liwenyip/adhoc/Appendix A - Figures/Diagrams/Buffer-Structure.gif

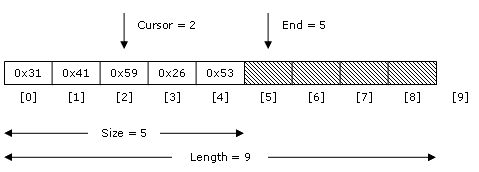
Appendix A - Figures/Diagrams/Buffer-Structure.gif
