liwenyip/adhoc/Appendix A - Figures/Diagrams/Manchester Signal.gif

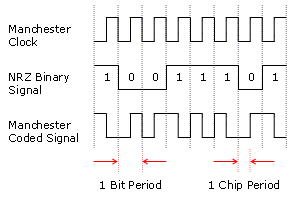
Appendix A - Figures/Diagrams/Manchester Signal.gif
