liwenyip/adhoc/Appendix A - Figures/Diagrams/Screenshot-Receive.gif

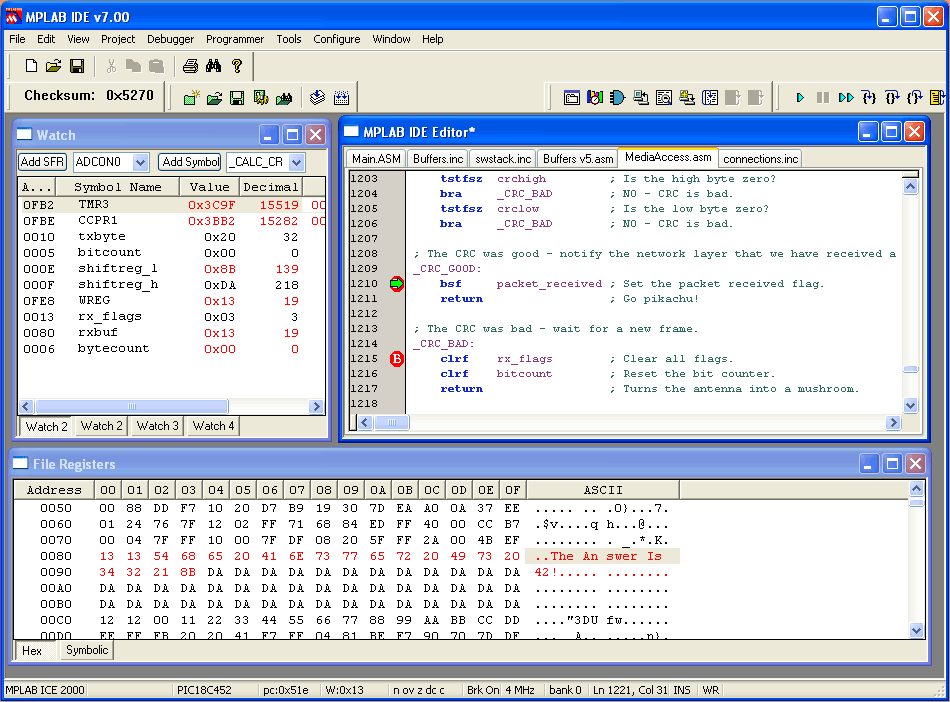
Appendix A - Figures/Diagrams/Screenshot-Receive.gif
