liwenyip/adhoc/Appendix A - Figures/Flowcharts/Decode.jpg

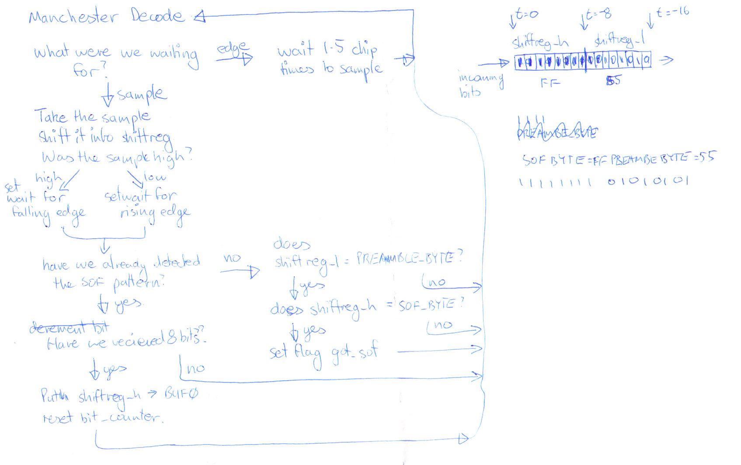
Appendix A - Figures/Flowcharts/Decode.jpg
