liwenyip/adhoc/Appendix A - Figures/Flowcharts/Encode.jpg

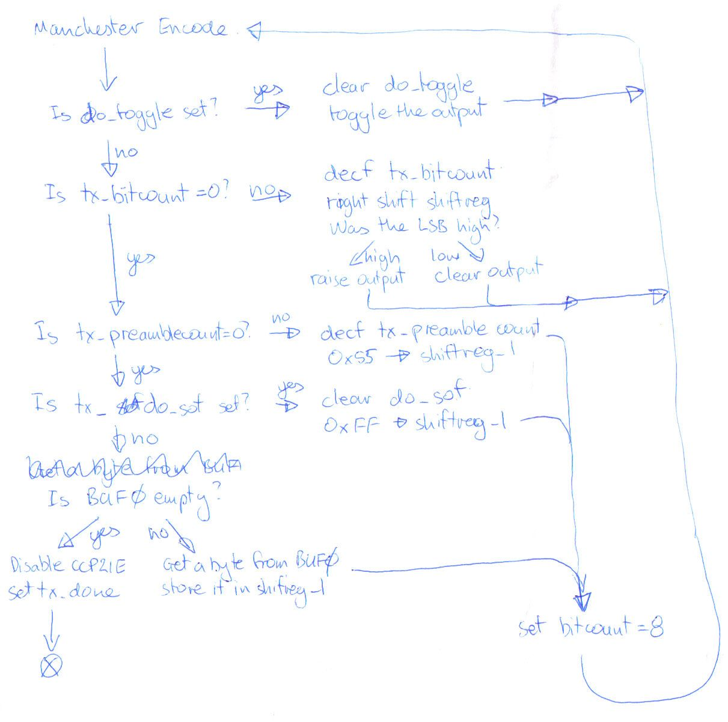
Appendix A - Figures/Flowcharts/Encode.jpg
