liwenyip/adhoc/Appendix A - Figures/Hardware/2004-Hardware-Block-Diagram.jpg

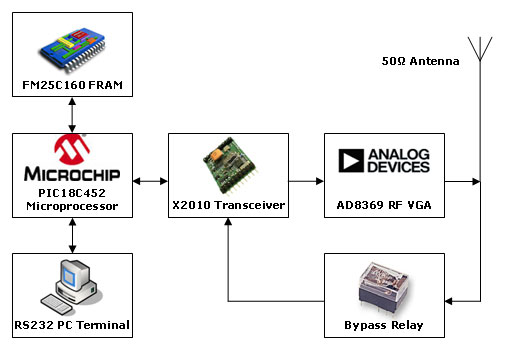
Appendix A - Figures/Hardware/2004-Hardware-Block-Diagram.jpg
