liwenyip/adhoc/Appendix A - Figures/Hardware/Emitter Follower.gif

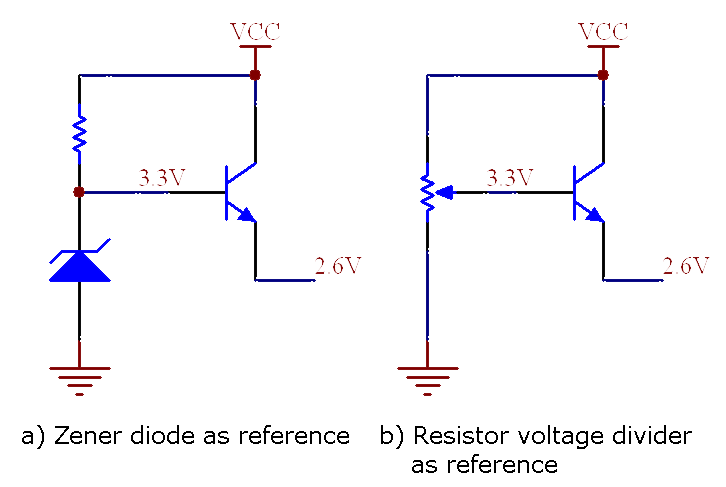
Appendix A - Figures/Hardware/Emitter Follower.gif
