liwenyip/adhoc/Appendix A - Figures/Hardware/OffSeparation-1.jpg

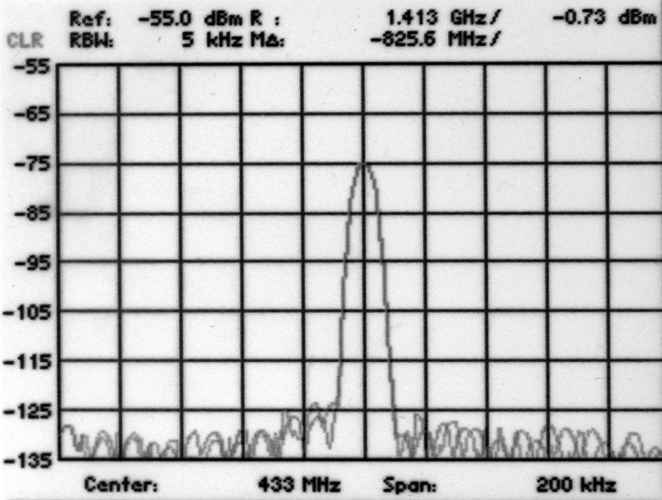
Appendix A - Figures/Hardware/OffSeparation-1.jpg
