liwenyip/adhoc/Appendix A - Figures/Hardware/OffSeparation-2.jpg

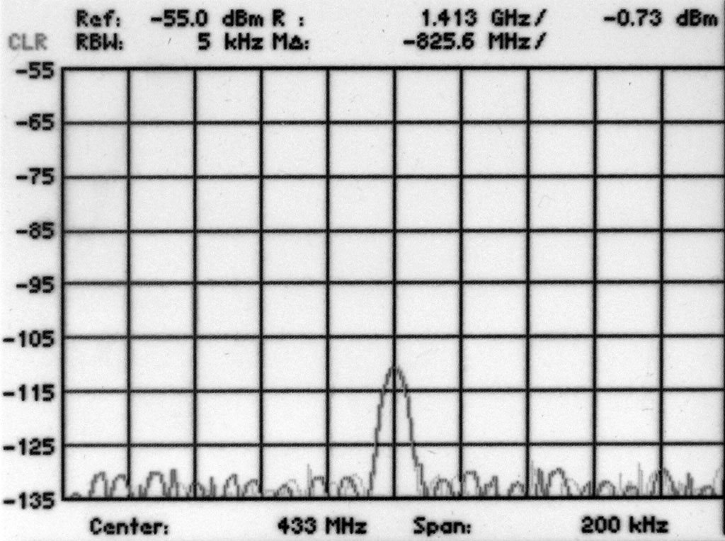
Appendix A - Figures/Hardware/OffSeparation-2.jpg
