liwenyip/adhoc/Appendix A - Figures/Hardware/PCB-Rev-3.jpg

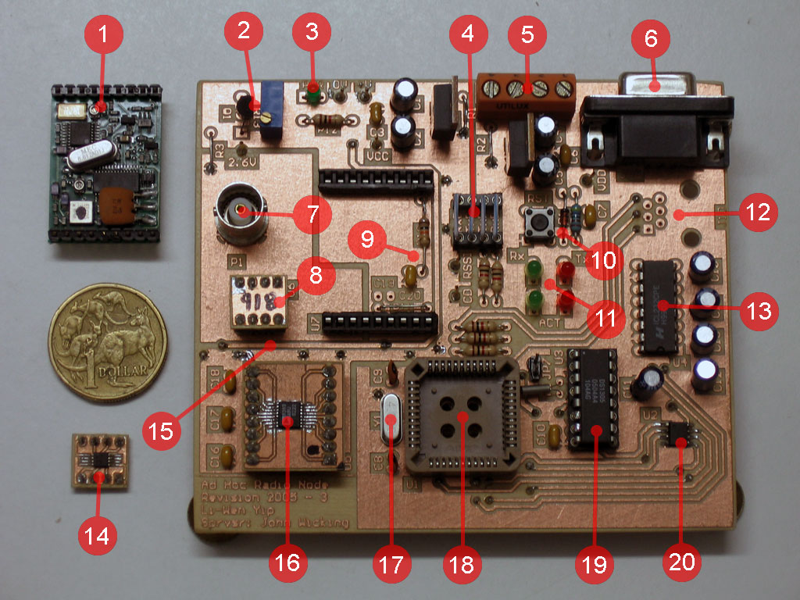
Appendix A - Figures/Hardware/PCB-Rev-3.jpg
