liwenyip/adhoc/Appendix A - Figures/Manchester Coding/Clock Detect Timing Diagram.gif

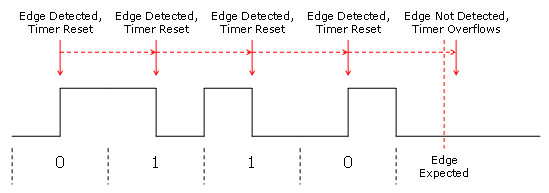
Appendix A - Figures/Manchester Coding/Clock Detect Timing Diagram.gif
