liwenyip/adhoc/Appendix A - Figures/Manchester Coding/Clock Drift.gif

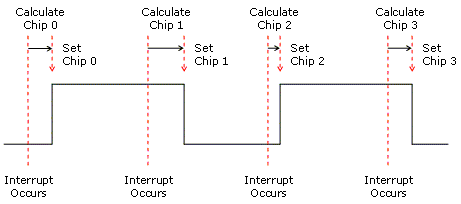
Appendix A - Figures/Manchester Coding/Clock Drift.gif
