liwenyip/adhoc/Appendix A - Figures/Manchester Coding/Sync Logic Timing Diagram.GIF

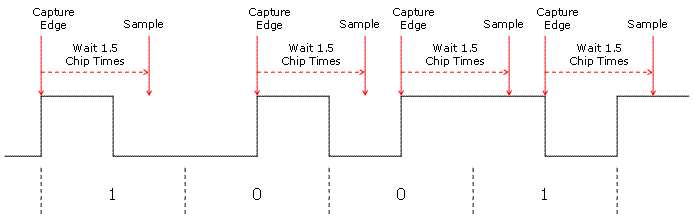
Appendix A - Figures/Manchester Coding/Sync Logic Timing Diagram.GIF
