liwenyip/adhoc/Appendix A - Figures/Photos/Carrier Detect, 1ms-div, 5v-div.jpg

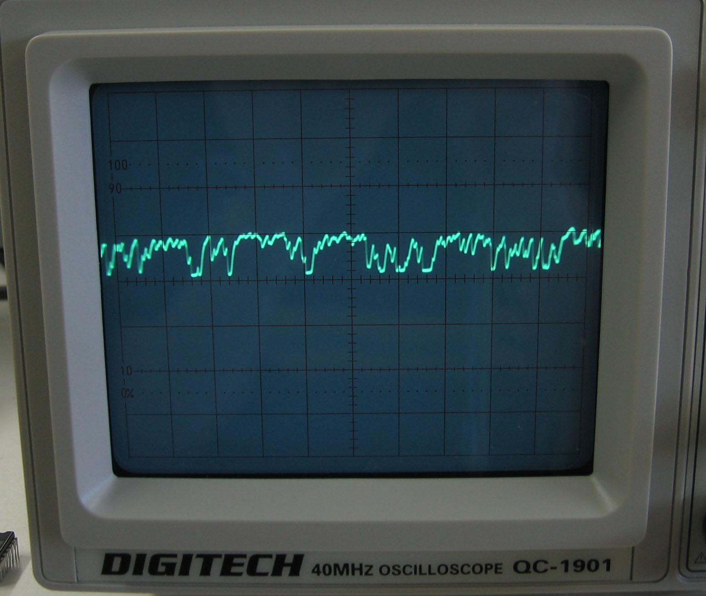
Appendix A - Figures/Photos/Carrier Detect, 1ms-div, 5v-div.jpg
