liwenyip/adhoc/Appendix A - Figures/Photos/PCB Revision 1.jpg

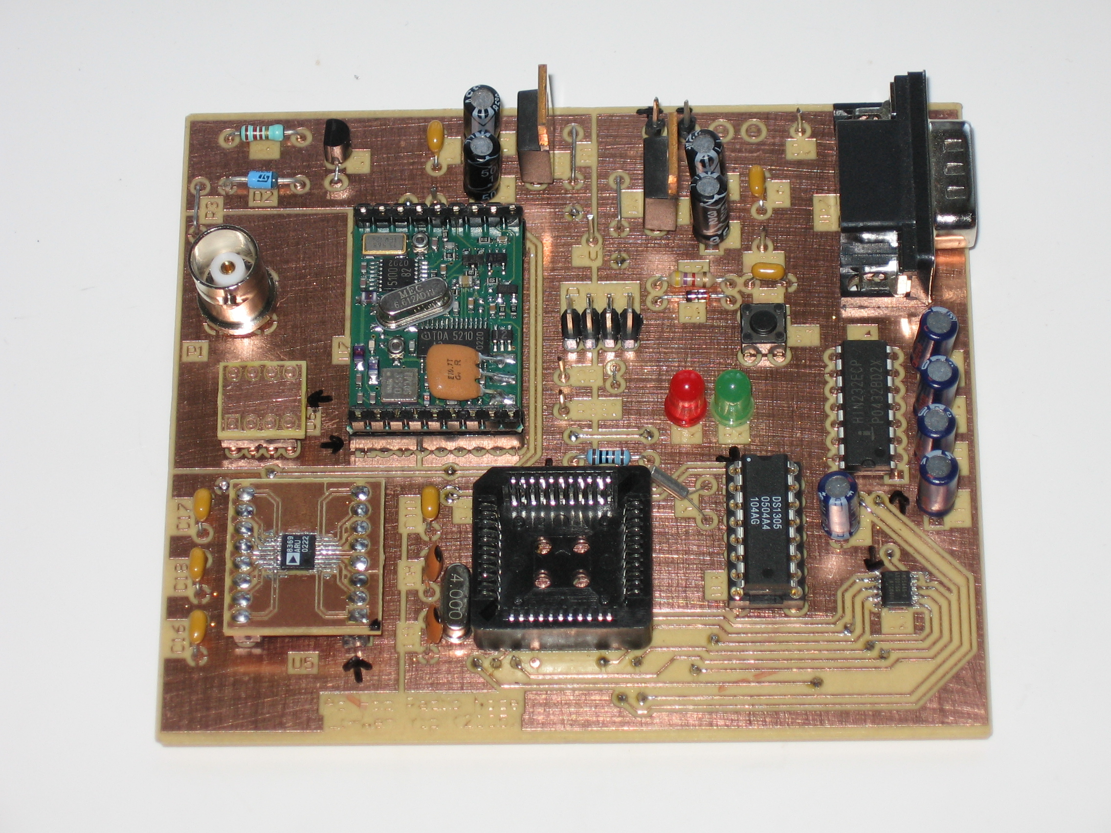
Appendix A - Figures/Photos/PCB Revision 1.jpg
