liwenyip/adhoc/Appendix A - Figures/Photos/Port separation 1.jpg

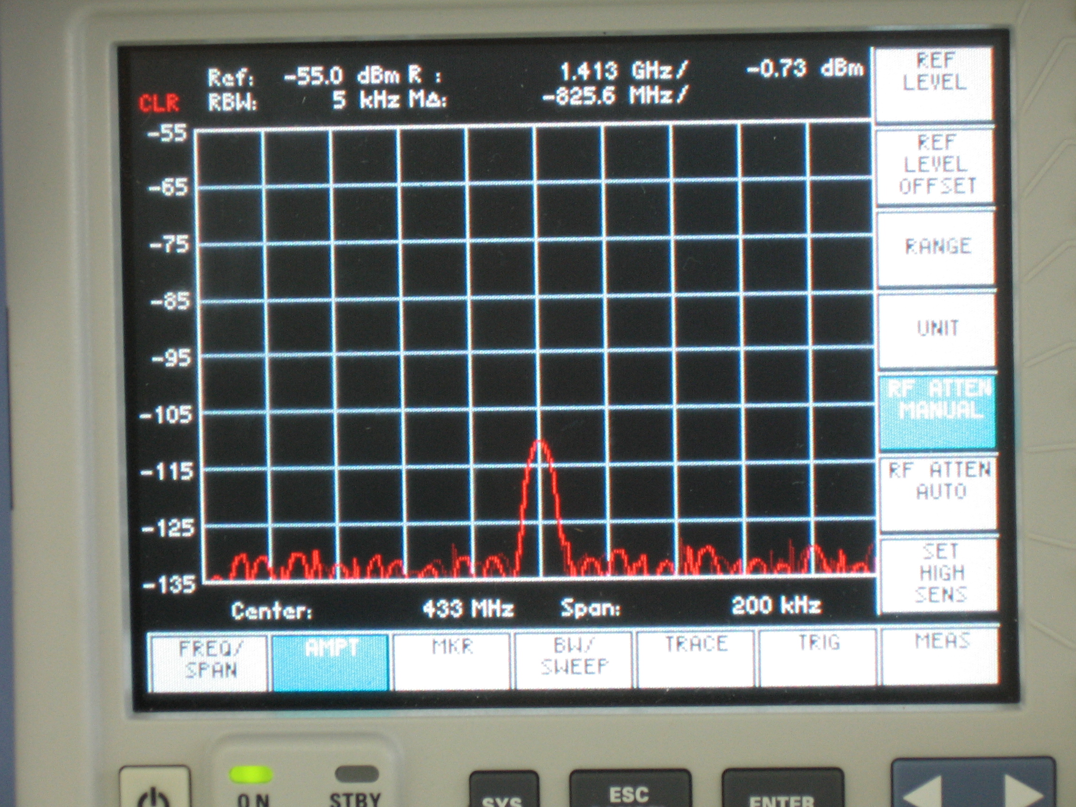
Appendix A - Figures/Photos/Port separation 1.jpg
