liwenyip/adhoc/Appendix A - Figures/Photos/Port separation 2.jpg

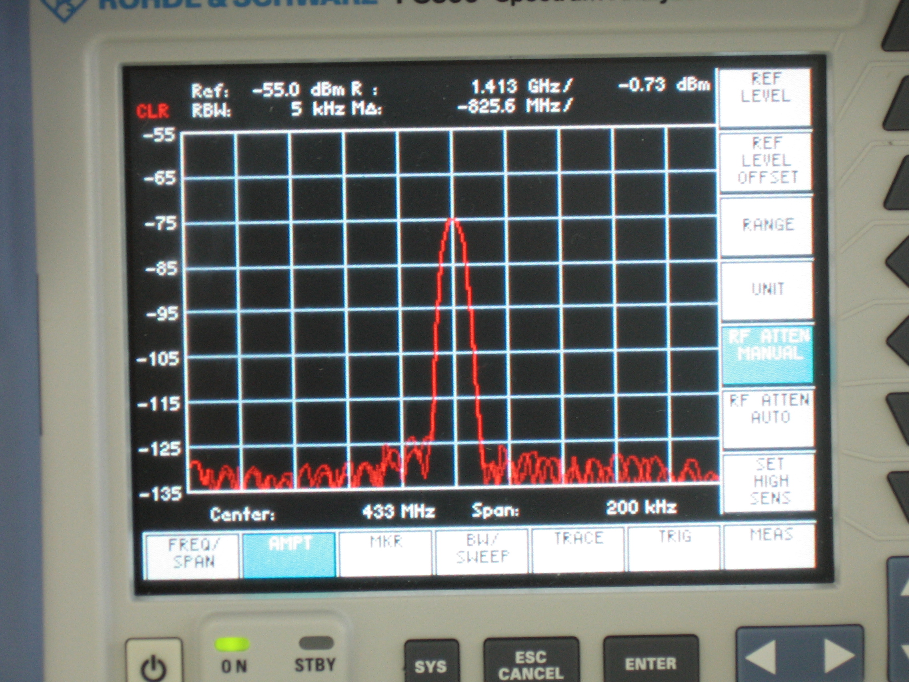
Appendix A - Figures/Photos/Port separation 2.jpg
