liwenyip/adhoc/Appendix A - Figures/Photos/RxD and CD without signal.jpg

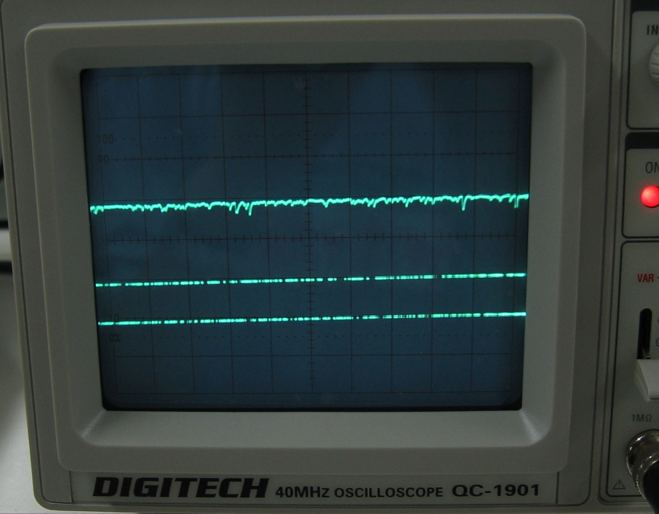
Appendix A - Figures/Photos/RxD and CD without signal.jpg
