liwenyip/adhoc/Appendix A - Figures/Photos/VGA $2.jpg

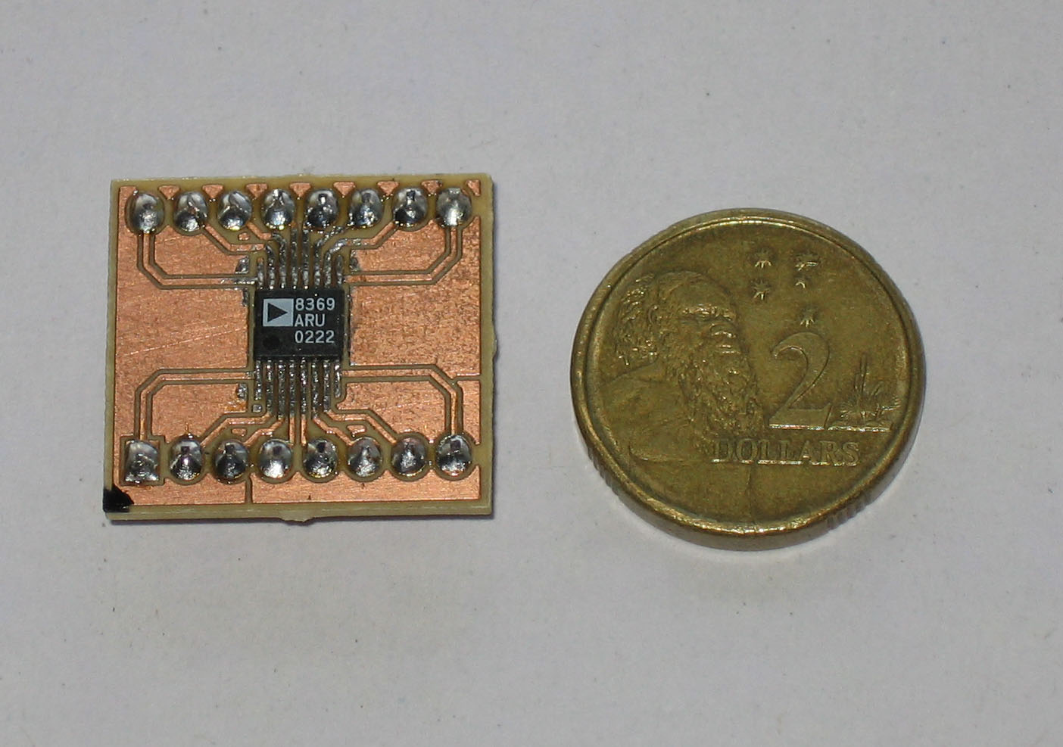
Appendix A - Figures/Photos/VGA $2.jpg
