liwenyip/adhoc/docs/images/adg918-insitu.jpg

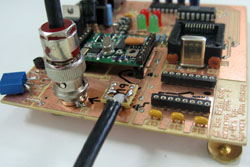
docs/images/adg918-insitu.jpg
