liwenyip/adhoc/docs/images/alloc-1.gif

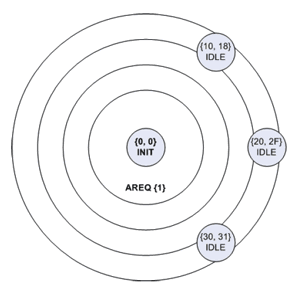
docs/images/alloc-1.gif
