liwenyip/adhoc/docs/images/alloc-2.gif

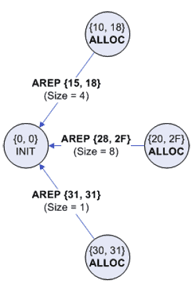
docs/images/alloc-2.gif
