liwenyip/adhoc/docs/images/alloc-3.gif

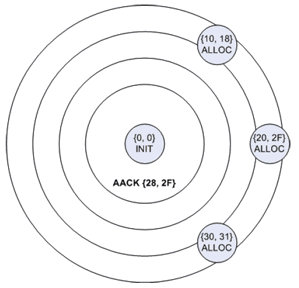
docs/images/alloc-3.gif
