liwenyip/adhoc/docs/images/alloc-4.gif

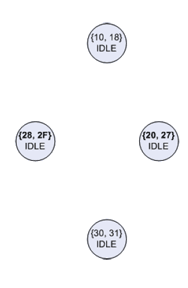
docs/images/alloc-4.gif
