liwenyip/adhoc/docs/images/block-diagram.gif

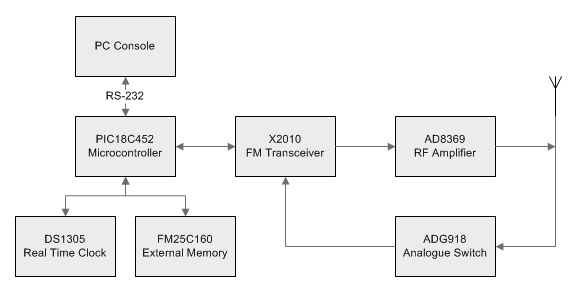
docs/images/block-diagram.gif
