liwenyip/adhoc/docs/images/clock-detect-graph.gif

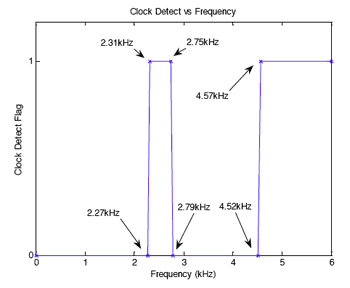
docs/images/clock-detect-graph.gif
