liwenyip/adhoc/docs/images/clock-detect.gif

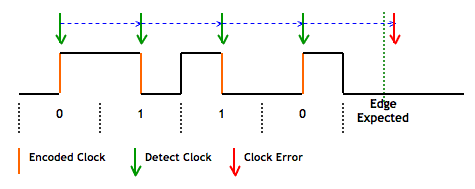
docs/images/clock-detect.gif
