liwenyip/adhoc/docs/images/davies-reef.jpg

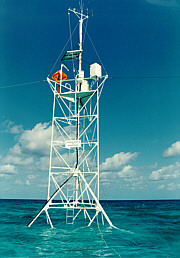
docs/images/davies-reef.jpg
