liwenyip/adhoc/docs/images/drop-shadows/shadow2-body.gif

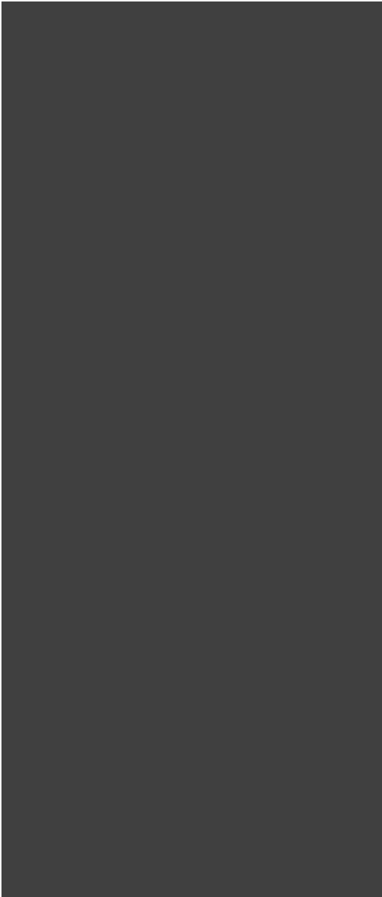
docs/images/drop-shadows/shadow2-body.gif
