liwenyip/adhoc/docs/images/hardware/ad8369-small.jpg

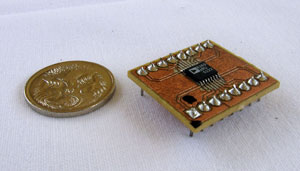
docs/images/hardware/ad8369-small.jpg
