liwenyip/adhoc/docs/images/hardware/coralsea.jpg

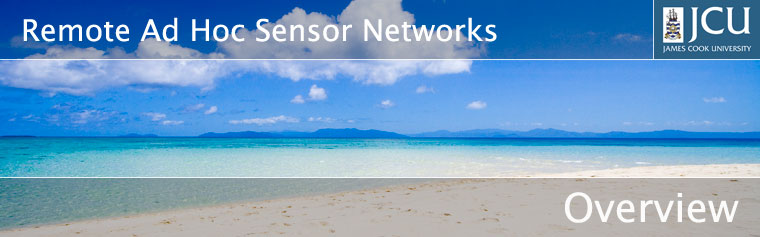
docs/images/hardware/coralsea.jpg
