liwenyip/adhoc/docs/images/hardware/ds1305-small.jpg

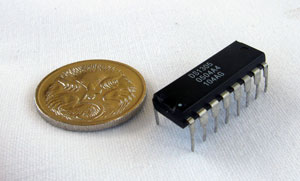
docs/images/hardware/ds1305-small.jpg
