liwenyip/adhoc/docs/images/hardware/ice2000-small.jpg

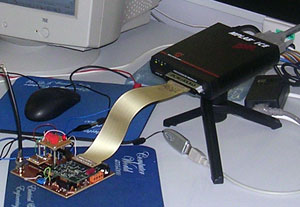
docs/images/hardware/ice2000-small.jpg
