liwenyip/adhoc/docs/images/manchester-decoding.gif

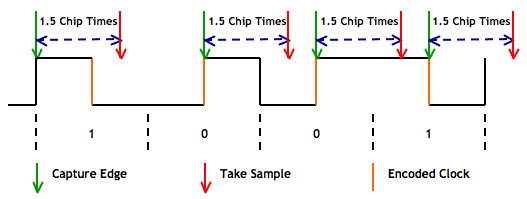
docs/images/manchester-decoding.gif
