liwenyip/adhoc/docs/images/manchester-encoding-slack.gif

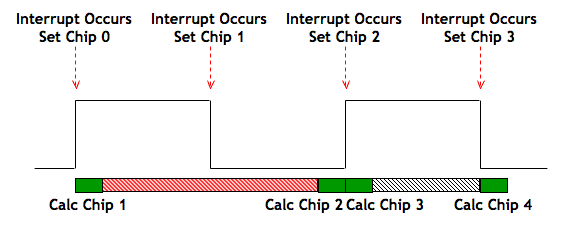
docs/images/manchester-encoding-slack.gif
