liwenyip/adhoc/docs/images/manchester-encoding.gif

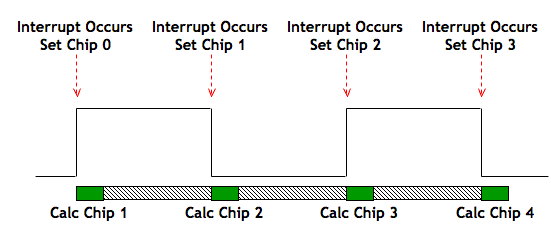
docs/images/manchester-encoding.gif
