liwenyip/adhoc/docs/images/preamblesampling-graph.gif

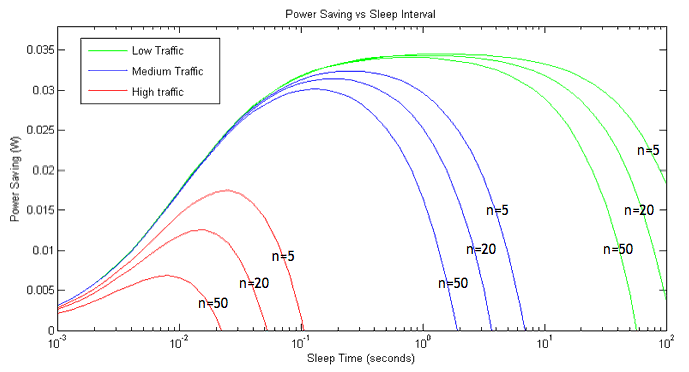
docs/images/preamblesampling-graph.gif
